vendolis/BeadSorter/STLs/2_Sequencer_base_modified_v2.stl

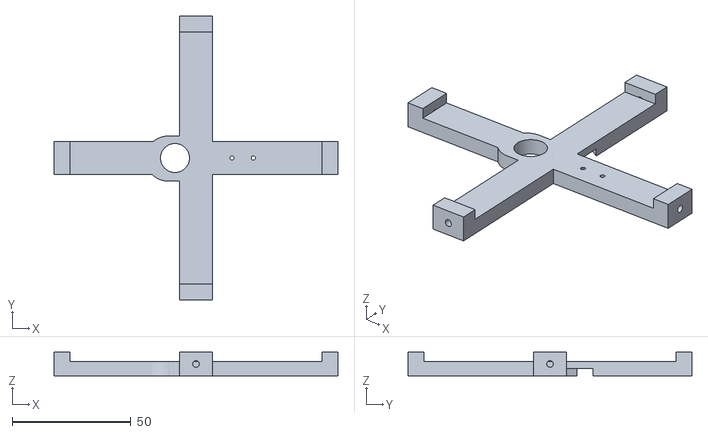
[picture p17: CAD file, 2026-03-10]
STLs/2_Sequencer_base_modified_v2.stl
119.6 x 119.6 x 10.0
