vendolis/BeadSorter/STLs/4-dispatcher-Tube-alignment-ring.stl

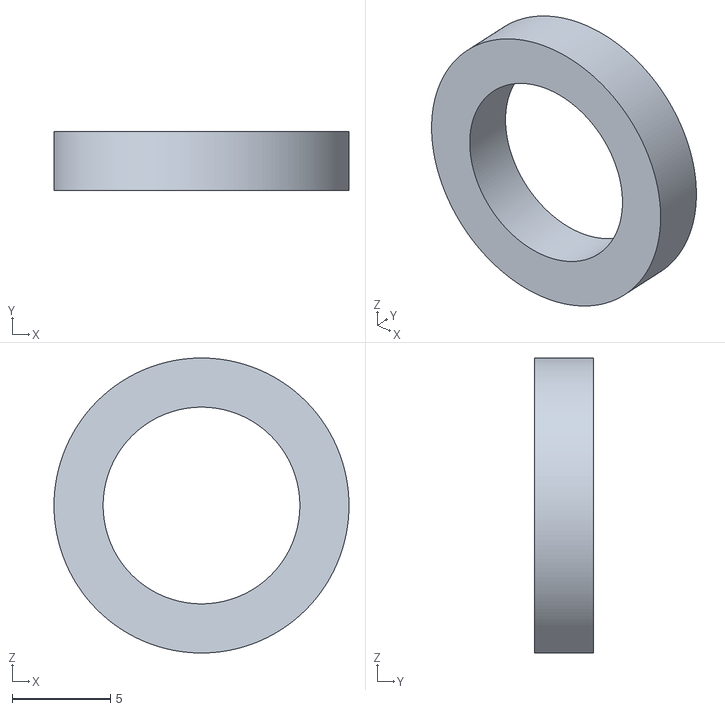
[picture p18: CAD file, 2026-03-10]
STLs/4-dispatcher-Tube-alignment-ring.stl
15.0 x 3.00 x 15.0
