vendolis/BeadSorter/STLs/4-dispatcher-Stepper-shaft.stl

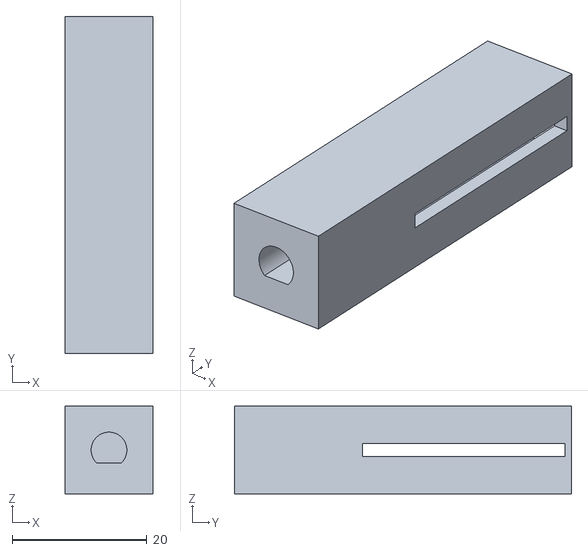
[picture p19: CAD file, 2026-03-10]
STLs/4-dispatcher-Stepper-shaft.stl
13.0 x 50.0 x 13.0
