vendolis/BeadSorter/STLs/5-outputs-slidePlate-holder_Typeb.stl

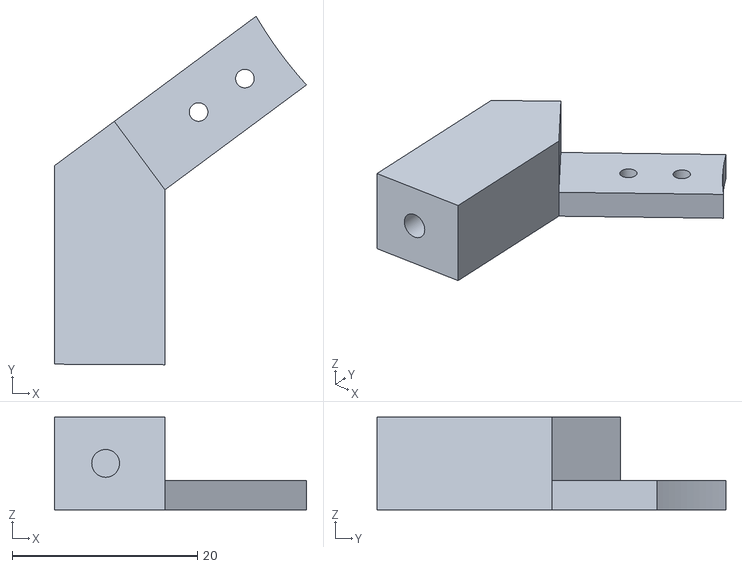
[picture p20: CAD file, 2026-03-10]
STLs/5-outputs-slidePlate-holder_Typeb.stl
27.2 x 37.6 x 10.0
