vendolis/BeadSorter/STLs/4-dispatcher-tube.stl

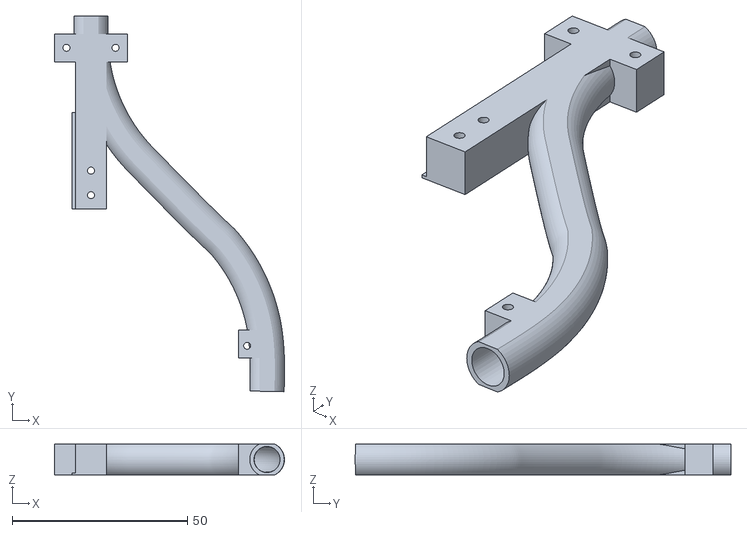
[picture p21: CAD file, 2026-03-09]
STLs/4-dispatcher-tube.stl
65.5 x 107.0 x 8.80
