vendolis/BeadSorter/STLs/4-dispatcher-tubehalf-1_modified.stl

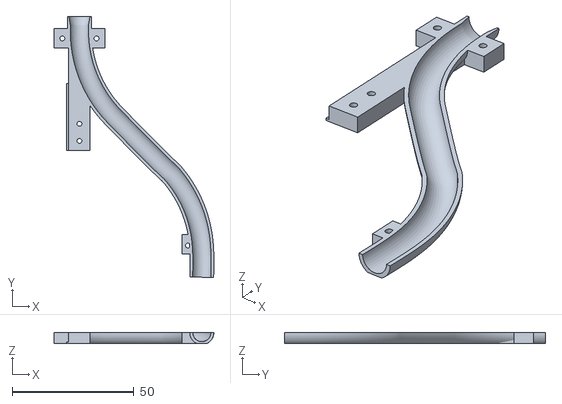
[picture p22: CAD file, 2026-03-09]
STLs/4-dispatcher-tubehalf-1_modified.stl
65.5 x 107.0 x 4.40
