vendolis/BeadSorter/STLs/3-analyzer-entry-tube_Extended.stl

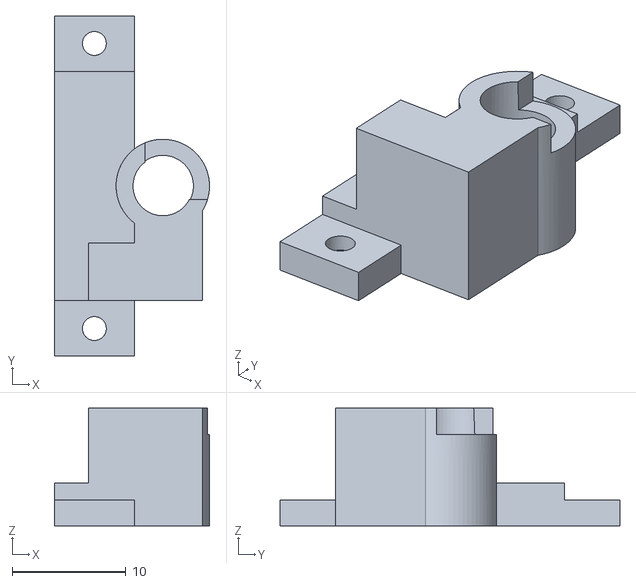
[picture p23: CAD file, 2026-03-09]
STLs/3-analyzer-entry-tube_Extended.stl
13.6 x 29.8 x 10.4
