vendolis/BeadSorter/STLs/2_Sequencer_tube_modified_v4_AntiStall.stl

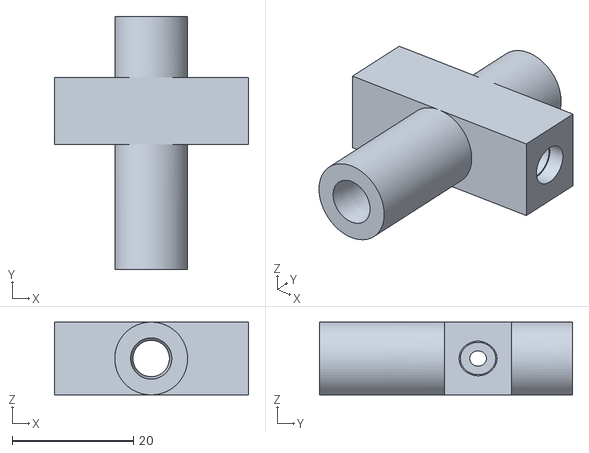
[picture p24: CAD file, 2026-03-09]
STLs/2_Sequencer_tube_modified_v4_AntiStall.stl
32.0 x 41.7 x 12.0
