vendolis/BeadSorter/STLs/SectionBracketPegs_v2.stl

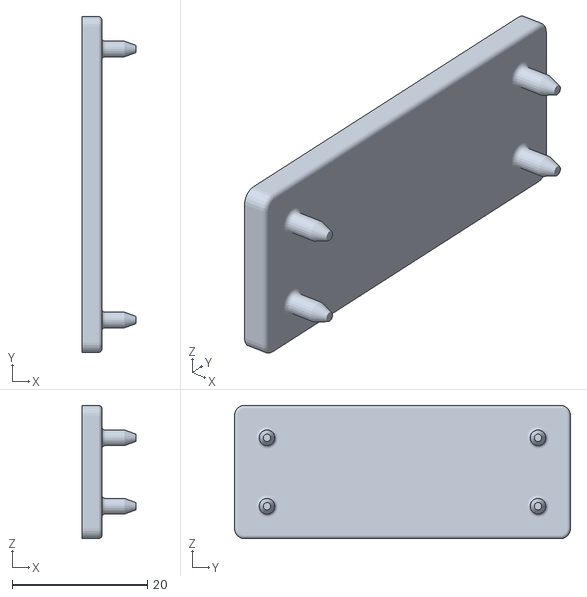
[picture p25: CAD file, 2026-03-09]
STLs/SectionBracketPegs_v2.stl
7.90 x 49.6 x 19.7
