vendolis/BeadSorter/STLs/0_HopperStick Holder v2.stl

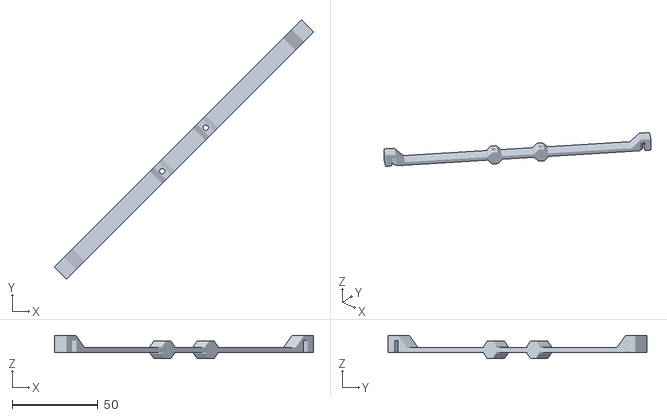
[picture p26: CAD file, 2026-03-09]
STLs/0_HopperStick Holder v2.stl
151.4 x 151.4 x 13.7
