vendolis/BeadSorter/STLs/SectionBracketHoles.stl

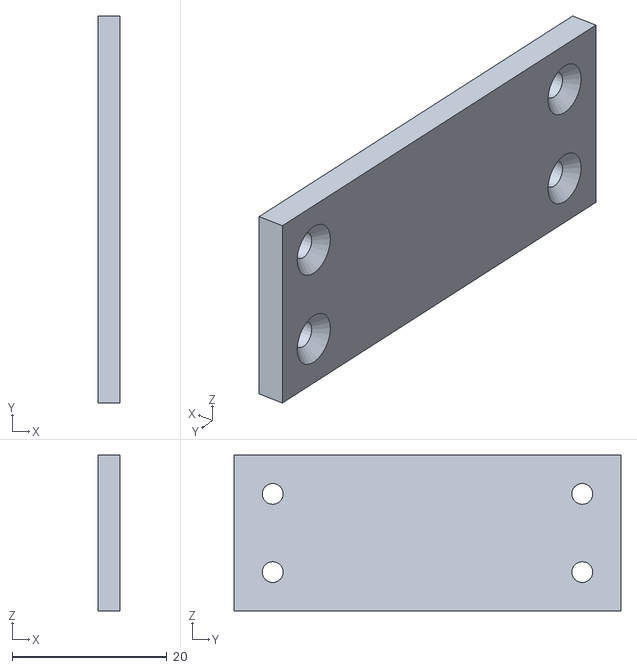
[picture p27: CAD file, 2026-03-09]
STLs/SectionBracketHoles.stl
2.90 x 50.0 x 20.1
