vendolis/BeadSorter/STLs/hopper-seq-plate-4_holes_modified_Glides.stl

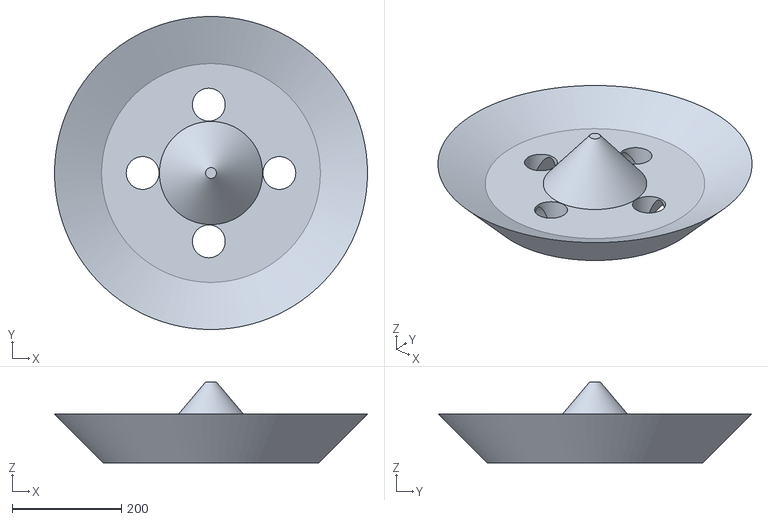
[picture p28: CAD file, 2026-03-09]
STLs/hopper-seq-plate-4_holes_modified_Glides.stl
572.3 x 572.3 x 147.9
