vendolis/BeadSorter/STLs/1-sequentializer-motor-holder.stl

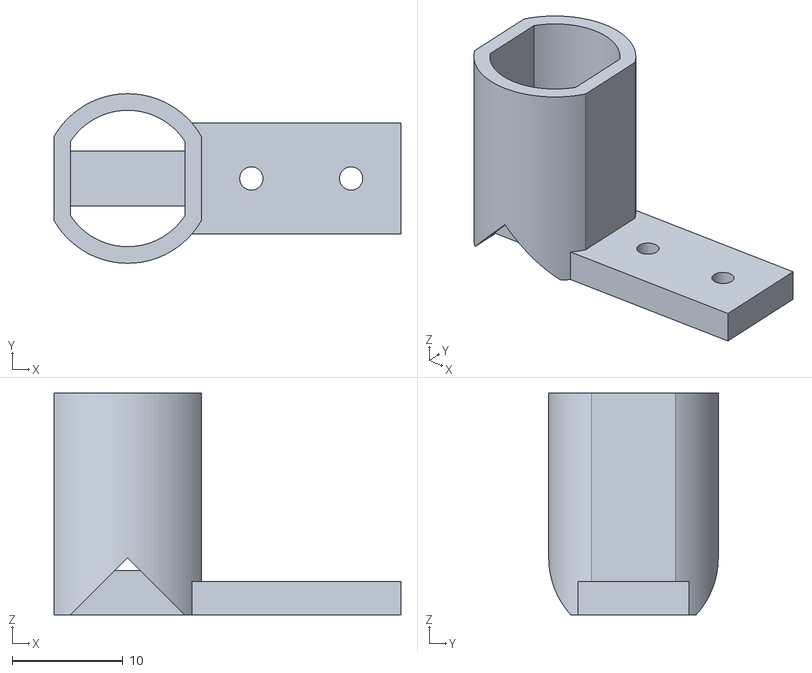
[picture p29: CAD file, 2026-03-05]
STLs/1-sequentializer-motor-holder.stl
31.3 x 15.3 x 20.0
