vendolis/BeadSorter/STLs/3-analyzer-ilc-top.stl

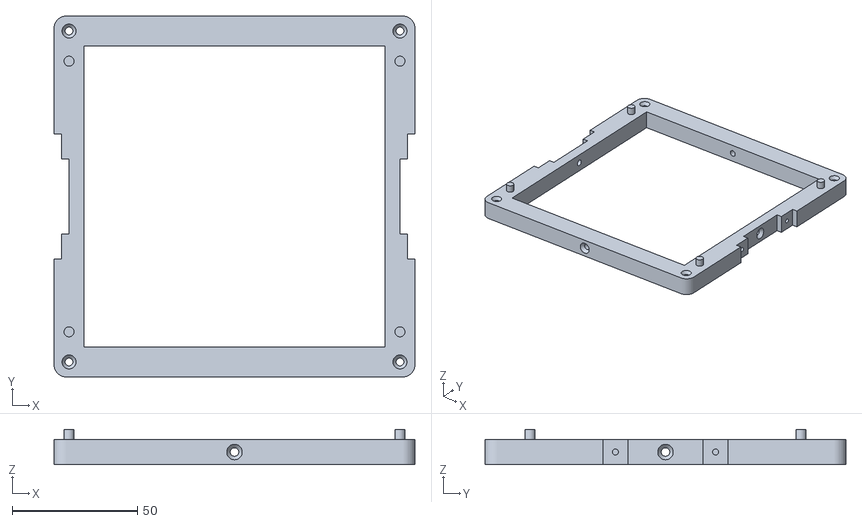
[picture p30: CAD file, 2026-03-05]
STLs/3-analyzer-ilc-top.stl
144.0 x 144.0 x 14.0
