vendolis/BeadSorter/STLs/3-analyzer-servo-holder.stl

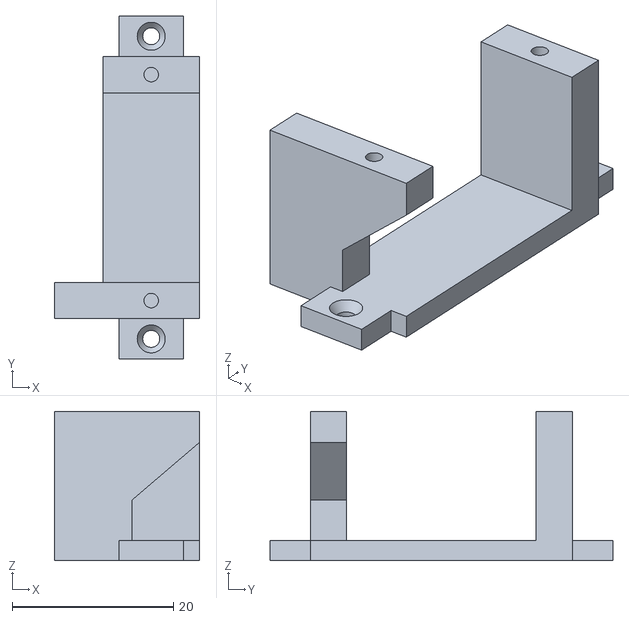
[picture p31: CAD file, 2026-03-05]
STLs/3-analyzer-servo-holder.stl
18.0 x 42.5 x 18.5
