vendolis/BeadSorter/STLs/0-hopper-seq-plate-4_holes_modified.stl

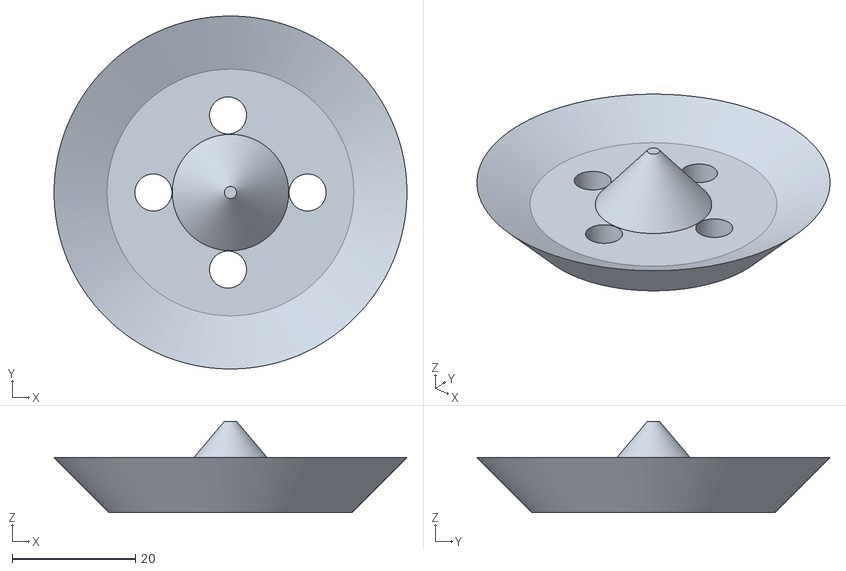
[picture p32: CAD file, 2026-03-05]
STLs/0-hopper-seq-plate-4_holes_modified.stl
57.2 x 57.2 x 14.8
