vendolis/BeadSorter/STLs/0-Hopper_Modified_Cleaned_up.stl

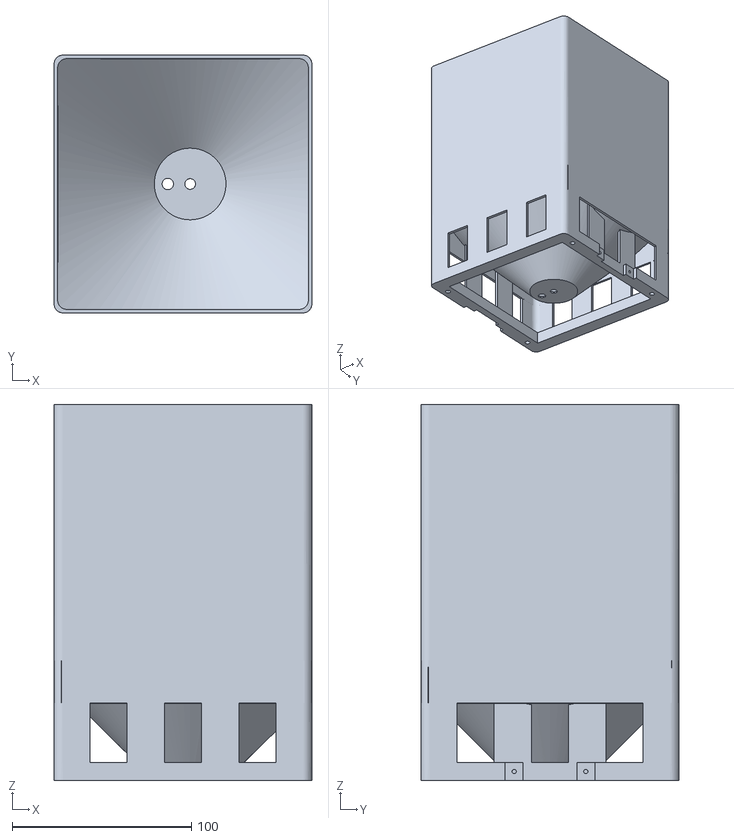
[picture p33: CAD file, 2026-03-05]
STLs/0-Hopper_Modified_Cleaned_up.stl
144.0 x 144.0 x 210.0
