vendolis/BeadSorter/STLs/4-dispatcher-tubehalf-2.stl

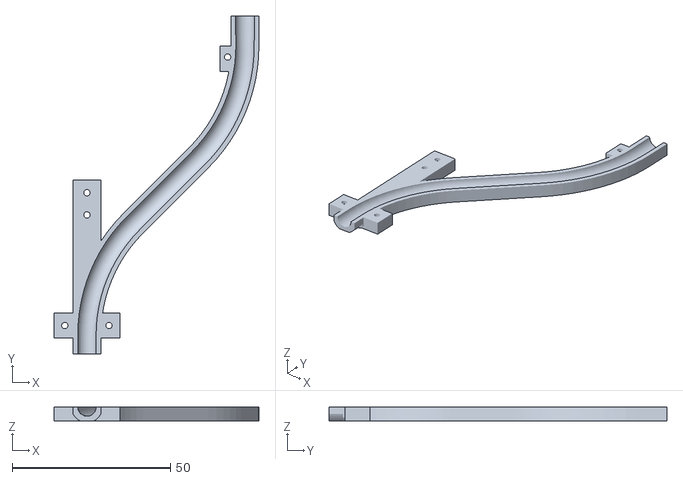
[picture p34: CAD file, 2026-03-05]
STLs/4-dispatcher-tubehalf-2.stl
64.8 x 106.9 x 4.40
