vendolis/BeadSorter/STLs/1-sequentializer-ilc-bottom.stl

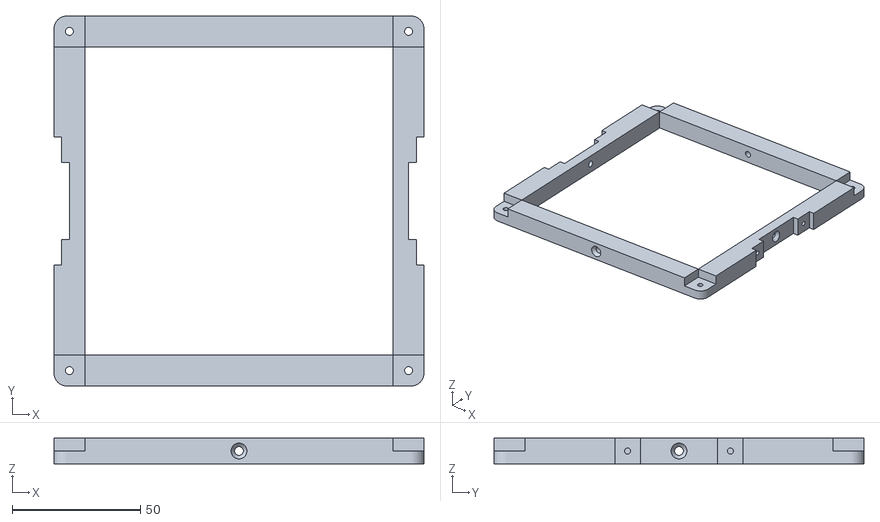
[picture p35: CAD file, 2026-03-05]
STLs/1-sequentializer-ilc-bottom.stl
144.0 x 144.0 x 10.0
