vendolis/BeadSorter/STLs/4-dispatcher-ilc-corner.stl

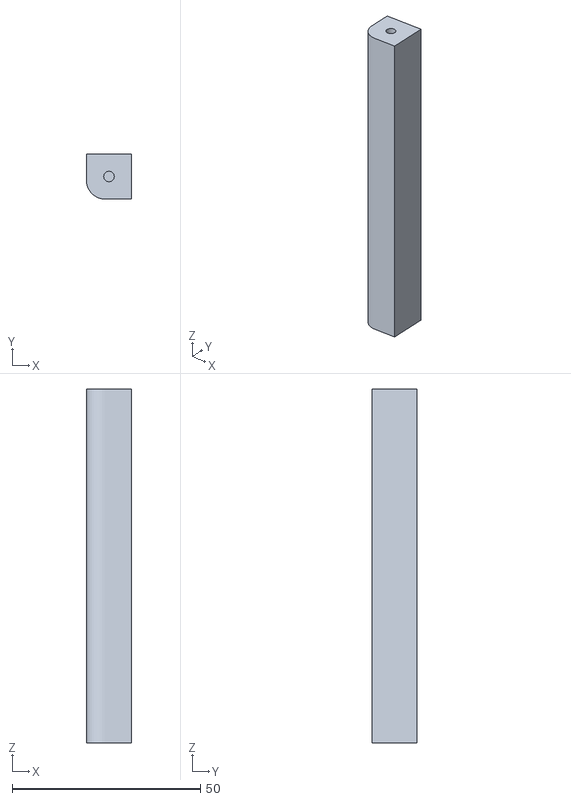
[picture p36: CAD file, 2026-03-05]
STLs/4-dispatcher-ilc-corner.stl
12.0 x 12.0 x 93.9
