vendolis/BeadSorter/STLs/4-dispatcher-ilc-bottom.stl

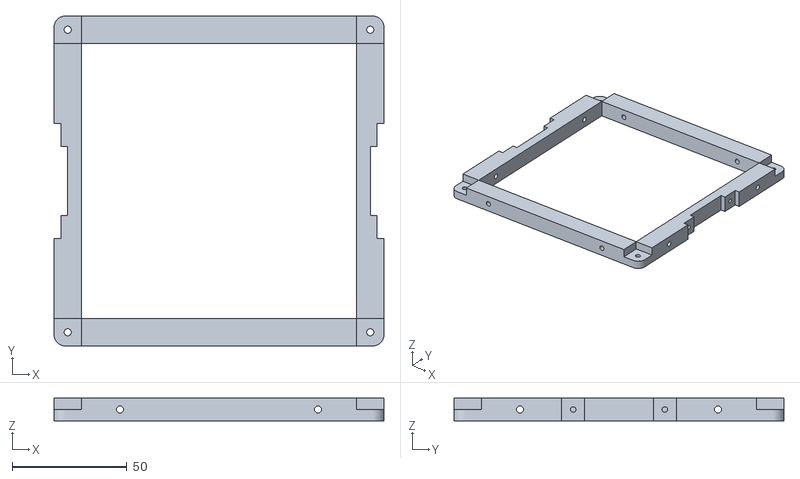
[picture p37: CAD file, 2026-03-05]
STLs/4-dispatcher-ilc-bottom.stl
144.0 x 144.0 x 10.0
