vendolis/BeadSorter/STLs/3-analyzer-exit-tube.stl

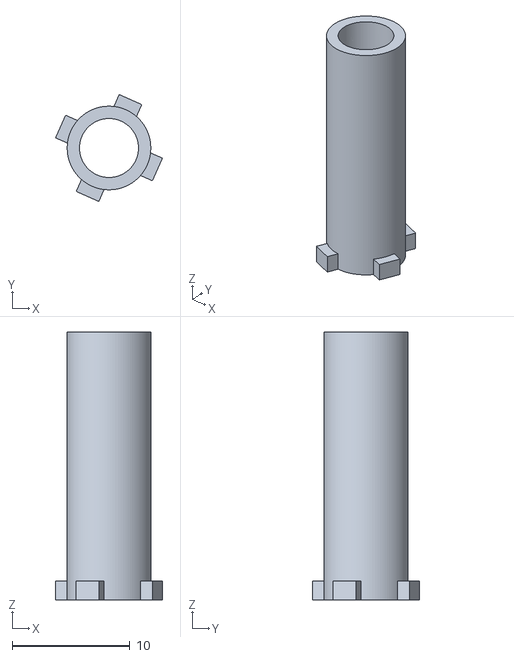
[picture p38: CAD file, 2026-03-05]
STLs/3-analyzer-exit-tube.stl
9.08 x 9.08 x 22.8
