vendolis/BeadSorter/STLs/5-outputs-ilc-corner.stl

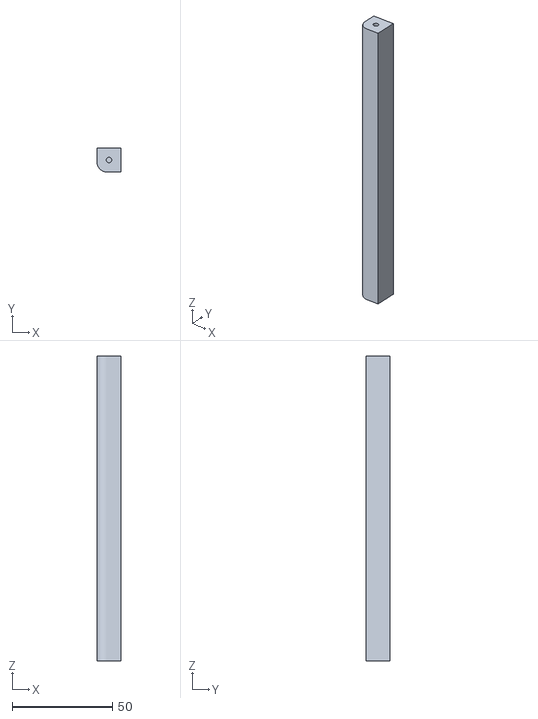
[picture p39: CAD file, 2026-03-05]
STLs/5-outputs-ilc-corner.stl
12.0 x 12.0 x 152.0
