vendolis/BeadSorter/STLs/3-analyzer-ilc-corner.stl

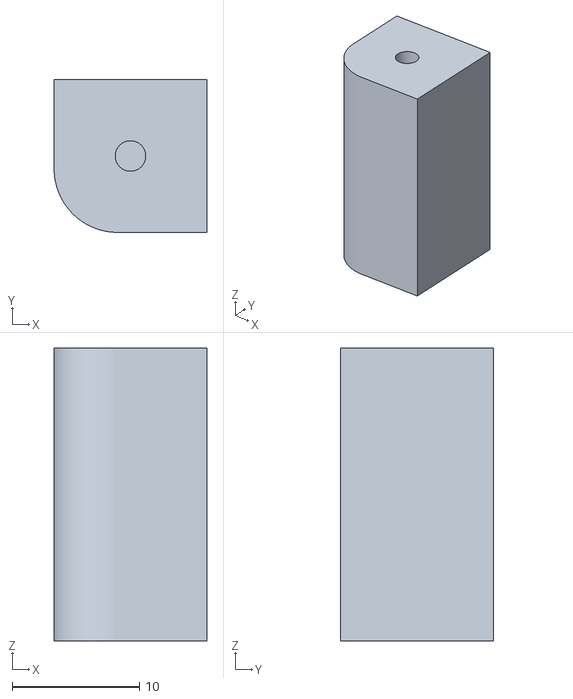
[picture p40: CAD file, 2026-03-05]
STLs/3-analyzer-ilc-corner.stl
12.0 x 12.0 x 23.1
