vendolis/BeadSorter/STLs/4-dispatcher-Stepper-shaft_alternative_3mm_square-Körper.stl

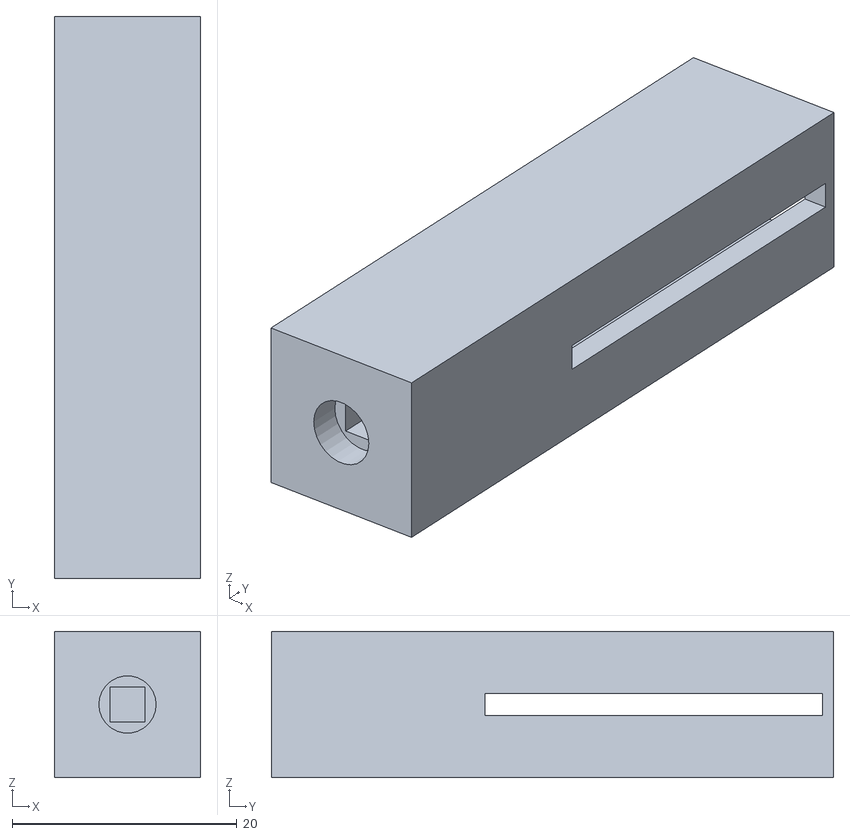
[picture p41: CAD file, 2026-03-05]
STLs/4-dispatcher-Stepper-shaft_alternative_3mm_square-Körper.stl
13.0 x 50.0 x 13.0
