vendolis/BeadSorter/STLs/3-analyzer-top-alignment.stl

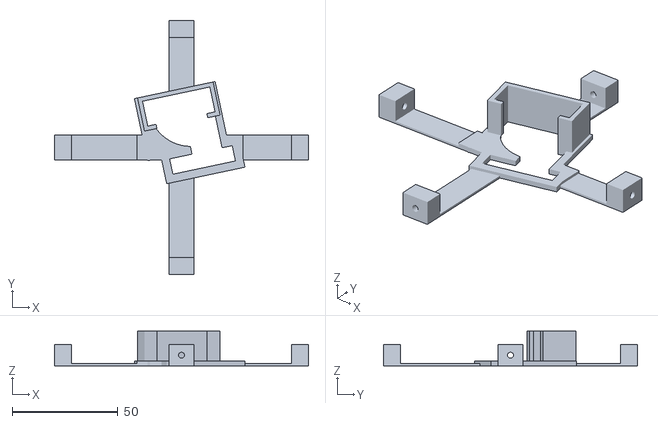
[picture p42: CAD file, 2026-03-05]
STLs/3-analyzer-top-alignment.stl
120.0 x 120.0 x 16.3
