vendolis/BeadSorter/STLs/0-hopper-seq-stopper.stl

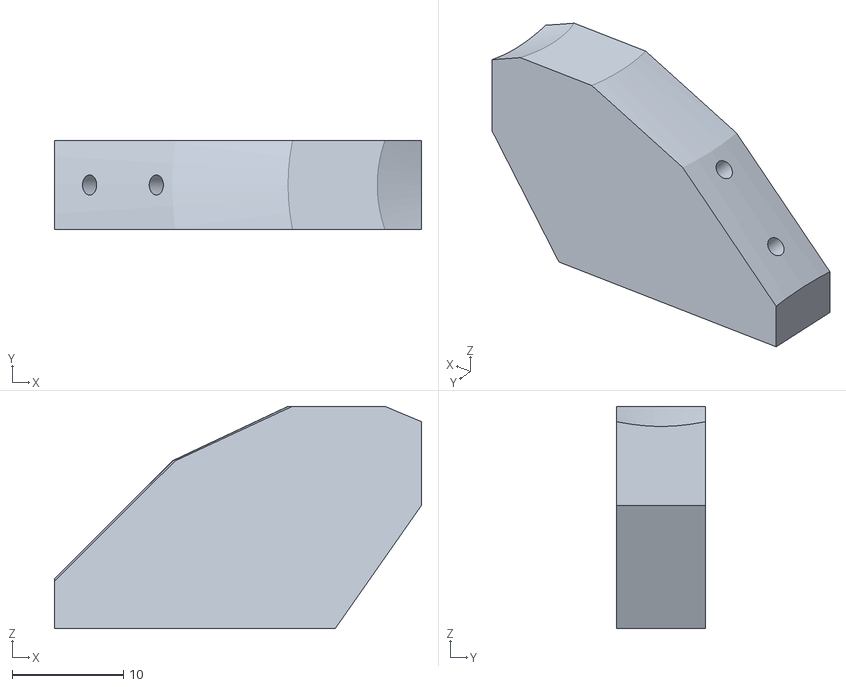
[picture p43: CAD file, 2026-03-05]
STLs/0-hopper-seq-stopper.stl
33.0 x 8.00 x 20.0
