vendolis/BeadSorter/STLs/4-dispatcher-tube-alignment.stl

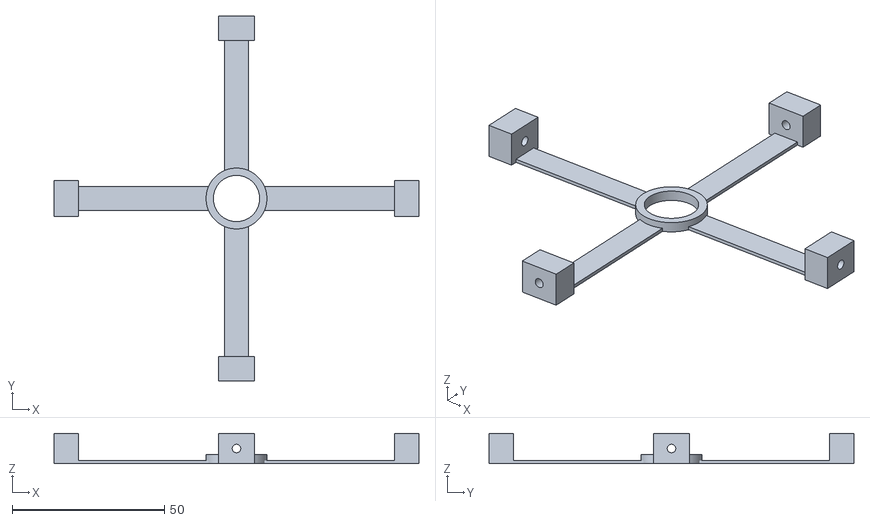
[picture p44: CAD file, 2026-03-05]
STLs/4-dispatcher-tube-alignment.stl
120.0 x 120.0 x 10.00
