vendolis/BeadSorter/classify_bead.py

import math


# Null scan baseline (empty chamber readings)
NULL_R = 498.1
NULL_G = 372.2
NULL_B = 244.2

# Max corrected RGB value (for scaling to 0-1)
RGB_MAX = 7931.9

# Normalization parameters (mean, std) for each feature
NORM_H_SIN = (0.470533, 0.356254)
NORM_H_COS = (0.488719, 0.642882)
NORM_S = (0.415330, 0.189916)
NORM_L = (0.191847, 0.165316)

# Representative points: (cluster_id, H_sin, H_cos, S, L)
# These are in the ORIGINAL (unnormalized) feature space.
REPRESENTATIVES = [
    (0, 0.981397, 0.191989, 0.458726, 0.240332),
    (0, 0.981061, 0.193701, 0.460193, 0.275317),
    (0, 0.966849, 0.255347, 0.448422, 0.228985),
    (0, 0.964240, 0.265030, 0.453953, 0.257856),
    (0, 0.964255, 0.264975, 0.455514, 0.185427),
    (1, 0.992586, 0.121547, 0.350025, 0.327574),
    (1, 0.939883, -0.341498, 0.265038, 0.354364),
    (1, 0.993824, 0.110967, 0.343485, 0.360605),
    (1, 0.988113, -0.153728, 0.352519, 0.313454),
    (1, 0.992391, 0.123125, 0.342631, 0.289752),
    (2, 0.891929, 0.452175, 0.231817, 0.381218),
    (2, 0.959937, 0.280216, 0.227916, 0.461589),
    (2, 0.929334, 0.369241, 0.230818, 0.440220),
    (2, 0.929025, 0.370016, 0.227779, 0.388530),
    (2, 0.960432, 0.278516, 0.241869, 0.412547),
    (3, 0.920954, -0.389671, 0.412970, 0.079211),
    (3, 0.972815, -0.231584, 0.352991, 0.100706),
    (3, 0.951580, -0.307401, 0.393046, 0.091566),
    (3, 0.987681, 0.156480, 0.333548, 0.020965),
    (3, 0.930853, -0.365393, 0.320121, 0.075996),
    (4, 0.585068, -0.810984, 0.380327, 0.184110),
    (4, 0.547077, -0.837082, 0.417597, 0.143074),
    (4, 0.544982, -0.838448, 0.393963, 0.157257),
    (4, 0.572035, -0.820230, 0.379107, 0.127504),
    (4, 0.583186, -0.812339, 0.404314, 0.165704),
    (5, 0.894990, -0.446087, 0.142407, 0.000857),
    (5, 0.894990, -0.446087, 0.124142, 0.000983),
    (5, 0.894990, -0.446087, 0.142407, 0.000857),
    (5, 0.894990, -0.446087, 0.142407, 0.000857),
    (5, 0.894990, -0.446087, 0.142407, 0.000857),
    (6, 0.922234, -0.386632, 0.074308, 0.000794),
    (6, 0.922234, -0.386632, 0.074308, 0.000794),
    (6, 0.922234, -0.386632, 0.074308, 0.000794),
    (6, 0.922234, -0.386632, 0.074308, 0.000794),
    (6, 0.922234, -0.386632, 0.074308, 0.000794),
    (7, 0.922234, -0.386632, 0.064124, 0.000920),
    (7, 0.922234, -0.386632, 0.064124, 0.000920),
    (7, 0.922234, -0.386632, 0.064124, 0.000920),
    (7, 0.922234, -0.386632, 0.064124, 0.000920),
    (7, 0.922234, -0.386632, 0.064124, 0.000920),
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
]

K_NEIGHBORS = 3


def _rgb_to_hls(r, g, b):
    """Convert RGB (0-1) to HLS. Returns (h, l, s)."""
    max_c = max(r, g, b)
    min_c = min(r, g, b)
    l = (max_c + min_c) / 2.0

    if max_c == min_c:
        return (0.0, l, 0.0)

    d = max_c - min_c
    s = d / (2.0 - max_c - min_c) if l > 0.5 else d / (max_c + min_c)

    if max_c == r:
        h = (g - b) / d + (6.0 if g < b else 0.0)
    elif max_c == g:
        h = (b - r) / d + 2.0
    else:
        h = (r - g) / d + 4.0
    h /= 6.0

    return (h, l, s)


def classify_bead(raw_r, raw_g, raw_b, raw_c):
    """
    Classify a bead from raw TCS34725 sensor values.

    Args:
        raw_r, raw_g, raw_b, raw_c: Raw RGBC readings from the sensor.

    Returns:
        Cluster ID (0-37), or -1 if the reading looks like an empty chamber.
    """
    # Subtract ambient light baseline
    r_corr = max(raw_r - NULL_R, 1.0)
    g_corr = max(raw_g - NULL_G, 1.0)
    b_corr = max(raw_b - NULL_B, 1.0)

    # Check if this is an empty chamber (values close to null baseline)
    if r_corr + g_corr + b_corr < 50:
        return -1

    # Scale to 0-1
    r01 = r_corr / RGB_MAX
    g01 = g_corr / RGB_MAX
    b01 = b_corr / RGB_MAX

    # Convert to HLS
    h, l, s = _rgb_to_hls(r01, g01, b01)

    # Encode hue on unit circle
    h_sin = math.sin(2.0 * math.pi * h)
    h_cos = math.cos(2.0 * math.pi * h)

    # Normalize features
    h_sin_n = (h_sin - NORM_H_SIN[0]) / NORM_H_SIN[1]
    h_cos_n = (h_cos - NORM_H_COS[0]) / NORM_H_COS[1]
    s_n = (s - NORM_S[0]) / NORM_S[1]
    l_n = (l - NORM_L[0]) / NORM_L[1]

    # Find k nearest neighbors by Euclidean distance
    distances = []
    for cluster_id, rep_h_sin, rep_h_cos, rep_s, rep_l in REPRESENTATIVES:
        # Normalize the representative point
        rh_sin_n = (rep_h_sin - NORM_H_SIN[0]) / NORM_H_SIN[1]
        rh_cos_n = (rep_h_cos - NORM_H_COS[0]) / NORM_H_COS[1]
        rs_n = (rep_s - NORM_S[0]) / NORM_S[1]
        rl_n = (rep_l - NORM_L[0]) / NORM_L[1]

        dist = math.sqrt(
            (h_sin_n - rh_sin_n) ** 2
            + (h_cos_n - rh_cos_n) ** 2
            + (s_n - rs_n) ** 2
            + (l_n - rl_n) ** 2
        )
        distances.append((dist, cluster_id))

    # Sort by distance, take k nearest
    distances.sort()
    neighbors = distances[:K_NEIGHBORS]

    # Distance-weighted vote
    votes = {}
    for dist, cluster_id in neighbors:
        weight = 1.0 / (dist + 1e-9)
        votes[cluster_id] = votes.get(cluster_id, 0.0) + weight

    return max(votes, key=votes.get)


if __name__ == "__main__":
    # Quick test with a few raw values from the log
    test_beads = [
        (993, 1529, 1222, 3789),    # Bead #0
        (4587, 2046, 1105, 7719),   # Bead #1
        (1586, 2418, 1969, 5961),   # Bead #2
        (1422, 1730, 1626, 4733),   # Bead #3
        (507, 381, 249, 1146),      # Null scan (should return -1)
    ]
    for r, g, b, c in test_beads:
        result = classify_bead(r, g, b, c)
        print(f"  R={r:5d} G={g:5d} B={b:5d} C={c:5d}  -> Cluster {result}")
