vendolis/BeadSorter/analyse_beads.py

#!/usr/bin/env python3
"""
analyse_beads.py — BeadSorter colour-space analysis tool
=========================================================

Reads the CSV produced by BeadCalibrate.ino and answers:
  1. Which TCS34725 gain setting gives clean, stable readings (no saturation,
     low intra-bead variance)?
  2. Which colour space — HSL, Chromaticity, Normalized RGB — best separates
     the scanned bead colours (maximum minimum pairwise distance)?
  3. What per-channel thresholds should go into BeadSorter.ino?

Usage:
  python analyse_beads.py  beads.csv
  python analyse_beads.py  beads.csv  --gain g16x
  python analyse_beads.py  beads.csv  --top 15

Output sections:
  • Saturation summary (per gain)
  • Per-bead mean values table (per gain)
  • Pairwise distance table — closest pairs first (per gain × colour space)
  • Cross-gain separability comparison
  • Threshold recommendations for BeadSorter.ino

Lines starting with '#' in the CSV are treated as comments and ignored.

Colour spaces compared
----------------------
  HSL       — H (circular), S, L  (same as BeadSorter.ino currently uses)
  HS        — H (circular), S only  (tests whether L helps or hurts)
  Chroma2   — chroma_r, chroma_g  (ambient-independent 2-D chromaticity)
  Chroma3   — chroma_r, chroma_g, chroma_b  (3-D; redundant since r+g+b=1
              but included for completeness)
  NormRGB   — R_norm, G_norm, B_norm  (clear-normalised, 0-255 scale)

Scale note — why raw distances cannot be compared across colour spaces
----------------------------------------------------------------------
  NormRGB operates on a 0-255 axis scale while all other spaces use 0-1,
  so raw Euclidean distances differ by a factor of up to ~255.  A NormRGB
  distance of 1.8 is NOT larger than a Chroma2 distance of 0.005 — they
  live on completely different rulers.

  The correct comparison metric is SNR (signal-to-noise ratio):

      SNR = min inter-bead distance / intra-bead noise RMS

  where noise RMS = sqrt(Σ avg_bead(σ_dim²)) across all dimensions of the
  space.  This is dimensionless and scale-independent.  An SNR > ~3 means
  beads are separated by more than 3× the typical sensor jitter — reliably
  classifiable.  All tables and the final recommendation use SNR.

Notes
-----
  - Chroma2 is usually best for this sensor because it is immune to absolute
    brightness variation and captures hue+saturation in a single 2-D metric.
  - HSL is good when hue spans a wide arc; it degrades for low-saturation
    colours where hue is poorly defined / noisy.
  - 16x gain often saturates bright reds/whites; if saturation % is high,
    prefer 4x or 1x for those beads.
"""

import sys
import io
import csv
import math
import collections
import itertools
import argparse
import statistics

# Ensure UTF-8 output on Windows terminals that default to cp1252.
if hasattr(sys.stdout, "reconfigure"):
    sys.stdout.reconfigure(encoding="utf-8", errors="replace")

# ── Circular hue helpers ──────────────────────────────────────────────────────

def hue_dist(h1: float, h2: float) -> float:
    """Shortest angular distance between two hue values in [0, 1]."""
    d = abs(h1 - h2)
    return min(d, 1.0 - d)


def circular_mean_hue(hues) -> float:
    """Compute the circular mean of hue values in [0, 1]."""
    sin_sum = sum(math.sin(h * 2.0 * math.pi) for h in hues)
    cos_sum = sum(math.cos(h * 2.0 * math.pi) for h in hues)
    angle = math.atan2(sin_sum, cos_sum)
    if angle < 0.0:
        angle += 2.0 * math.pi
    return angle / (2.0 * math.pi)


# ── Distance functions (one per colour space) ─────────────────────────────────

def dist_hsl(a: dict, b: dict) -> float:
    dh = hue_dist(a["H"], b["H"])
    return math.sqrt(dh**2 + (a["S"] - b["S"])**2 + (a["L"] - b["L"])**2)


def dist_hs(a: dict, b: dict) -> float:
    """HSL without L — tests whether lightness adds discriminating power."""
    dh = hue_dist(a["H"], b["H"])
    return math.sqrt(dh**2 + (a["S"] - b["S"])**2)


def dist_chroma2(a: dict, b: dict) -> float:
    """2-D chromaticity: chroma_r and chroma_g only (chroma_b = 1 - r - g)."""
    return math.sqrt((a["chroma_r"] - b["chroma_r"])**2 +
                     (a["chroma_g"] - b["chroma_g"])**2)


def dist_chroma3(a: dict, b: dict) -> float:
    """3-D chromaticity: all three normalised colour fractions."""
    return math.sqrt((a["chroma_r"] - b["chroma_r"])**2 +
                     (a["chroma_g"] - b["chroma_g"])**2 +
                     (a["chroma_b"] - b["chroma_b"])**2)


def dist_normrgb(a: dict, b: dict) -> float:
    """Euclidean distance in clear-normalised RGB space (0-255 scale)."""
    return math.sqrt((a["R_norm"] - b["R_norm"])**2 +
                     (a["G_norm"] - b["G_norm"])**2 +
                     (a["B_norm"] - b["B_norm"])**2)


# Ordered dict so the table columns stay consistent.
COLOR_SPACES = {
    "HSL":     dist_hsl,
    "HS":      dist_hs,
    "Chroma2": dist_chroma2,
    "Chroma3": dist_chroma3,
    "NormRGB": dist_normrgb,
}

# std_* fields that contribute to each space's noise RMS estimate.
# Must match the dimensions used in the corresponding dist_* function.
CS_STD_FIELDS = {
    "HSL":     ["std_H", "std_S", "std_L"],
    "HS":      ["std_H", "std_S"],
    "Chroma2": ["std_chroma_r", "std_chroma_g"],
    "Chroma3": ["std_chroma_r", "std_chroma_g", "std_chroma_b"],
    "NormRGB": ["std_R_norm", "std_G_norm", "std_B_norm"],
}


def cs_noise_rms(means: dict, cs_name: str) -> float:
    """
    Typical intra-bead positional noise magnitude for a given colour space.

    Computed as sqrt(Σ_dim  mean_bead(σ_dim²)) — the expected Euclidean
    distance between a bead's true colour-space position and one noisy
    measurement.  Scale-aware: directly comparable to the same space's
    dist_* output, so dividing distance / noise_rms gives a dimensionless
    SNR that can be compared across colour spaces and gains.

    Only beads with ≥2 samples (which carry std fields) contribute.
    Returns NaN if none qualify.
    """
    std_fields = CS_STD_FIELDS[cs_name]
    qualifying = [m for m in means.values() if std_fields[0] in m]
    if not qualifying:
        return float("nan")
    return math.sqrt(sum(
        statistics.mean(m[f] ** 2 for m in qualifying)
        for f in std_fields
    ))

# ── CSV parsing ───────────────────────────────────────────────────────────────

def parse_csv(path: str) -> list:
    rows = []
    with open(path, newline="", encoding="utf-8") as fh:
        lines = fh.readlines()

    # Find the actual CSV header — first non-comment line containing 'bead,gain'.
    header_idx = None
    for i, line in enumerate(lines):
        if line.lstrip().startswith("#"):
            continue
        if "bead" in line and "gain" in line and "sample" in line:
            header_idx = i
            break
    if header_idx is None:
        return rows

    # Keep header + data lines; drop comment lines.
    data_lines = [lines[header_idx]] + [
        l for l in lines[header_idx + 1:]
        if not l.lstrip().startswith("#")
    ]
    reader = csv.DictReader(io.StringIO("".join(data_lines)))
    for row in reader:
            try:
                entry = {
                    "bead":     int(row["bead"]),
                    "gain":     row["gain"].strip(),
                    "sample":   int(row["sample"]),
                    "R_raw":    int(row["R_raw"]),
                    "G_raw":    int(row["G_raw"]),
                    "B_raw":    int(row["B_raw"]),
                    "C_raw":    int(row["C_raw"]),
                    "sat":      int(row["saturated"]) != 0,
                    "R_norm":   float(row["R_norm"]),
                    "G_norm":   float(row["G_norm"]),
                    "B_norm":   float(row["B_norm"]),
                    "chroma_r": float(row["chroma_r"]),
                    "chroma_g": float(row["chroma_g"]),
                    "chroma_b": float(row["chroma_b"]),
                    "H":        float(row["H"]),
                    "S":        float(row["S"]),
                    "L":        float(row["L"]),
                }
                rows.append(entry)
            except (KeyError, ValueError):
                pass  # skip malformed rows silently
    return rows

# ── Per-bead statistics ───────────────────────────────────────────────────────

SCALAR_FIELDS = ["R_norm", "G_norm", "B_norm",
                 "chroma_r", "chroma_g", "chroma_b",
                 "S", "L"]


def compute_bead_means(rows: list, gain: str) -> dict:
    """
    Return {bead_id: mean_dict} for the given gain, excluding saturated rows.
    mean_dict contains mean values for every colour field plus 'n' (sample count).
    """
    filtered = [r for r in rows if r["gain"] == gain and not r["sat"]]
    by_bead = collections.defaultdict(list)
    for r in filtered:
        by_bead[r["bead"]].append(r)

    means = {}
    for bead, rs in sorted(by_bead.items()):
        m = {"bead": bead, "n": len(rs)}
        m["H"] = circular_mean_hue([r["H"] for r in rs])
        for f in SCALAR_FIELDS:
            m[f] = statistics.mean(r[f] for r in rs)
        # Intra-bead noise (std dev); needs ≥ 2 samples.
        if len(rs) >= 2:
            m["std_H"] = statistics.stdev(r["H"] for r in rs)
            for f in SCALAR_FIELDS:
                m[f"std_{f}"] = statistics.stdev(r[f] for r in rs)
        means[bead] = m
    return means


# ── Pairwise analysis ─────────────────────────────────────────────────────────

def pairwise_distances(means: dict, dist_fn) -> list:
    """Return sorted list of (distance, bead_a, bead_b) for all pairs."""
    pairs = [
        (dist_fn(means[a], means[b]), a, b)
        for a, b in itertools.combinations(sorted(means.keys()), 2)
    ]
    pairs.sort()
    return pairs


def suggest_hsl_thresholds(means: dict) -> tuple:
    """
    Return (thH, thS, thL) as half the minimum per-channel inter-bead gap.
    This is the tightest threshold that does not split any pair.

    Note: this is computed per-channel independently (AND-logic matching).
    A pair separated by one channel won't be penalised in another channel's gap.
    """
    beads = sorted(means.keys())
    min_dH = min_dS = min_dL = float("inf")
    for a, b in itertools.combinations(beads, 2):
        dh = hue_dist(means[a]["H"], means[b]["H"])
        ds = abs(means[a]["S"] - means[b]["S"])
        dl = abs(means[a]["L"] - means[b]["L"])
        if dh < min_dH:
            min_dH = dh
        if ds < min_dS:
            min_dS = ds
        if dl < min_dL:
            min_dL = dl
    return min_dH / 2.0, min_dS / 2.0, min_dL / 2.0


def suggest_chroma_threshold(means: dict) -> float:
    """Return half the minimum 2-D chromaticity distance between any pair."""
    beads = sorted(means.keys())
    min_d = min(
        dist_chroma2(means[a], means[b])
        for a, b in itertools.combinations(beads, 2)
    )
    return min_d / 2.0


# ── Keep-together / keep-apart feasibility ───────────────────────────────────

def compute_hsl_deviations(rows: list, gain: str, means: dict) -> dict:
    """
    For each bead, compute the maximum per-channel deviation of any individual
    sample from the bead's computed mean (H circular, S/L linear).

    This is the MINIMUM threshold required to keep all readings of the same
    bead in the same bucket.

    Returns {bead: {'dH': float, 'dS': float, 'dL': float}}.
    """
    filtered = [r for r in rows if r["gain"] == gain and not r["sat"]]
    by_bead = collections.defaultdict(list)
    for r in filtered:
        by_bead[r["bead"]].append(r)

    devs = {}
    for bead, rs in by_bead.items():
        if bead not in means:
            continue
        m = means[bead]
        devs[bead] = {
            "dH": max(hue_dist(r["H"], m["H"]) for r in rs),
            "dS": max(abs(r["S"]  - m["S"])     for r in rs),
            "dL": max(abs(r["L"]  - m["L"])     for r in rs),
        }
    return devs


def compute_chroma2_deviations(rows: list, gain: str, means: dict) -> dict:
    """
    For each bead, compute the maximum 2-D chromaticity distance of any
    individual sample from the bead's mean.

    Returns {bead: float}.
    """
    filtered = [r for r in rows if r["gain"] == gain and not r["sat"]]
    by_bead = collections.defaultdict(list)
    for r in filtered:
        by_bead[r["bead"]].append(r)

    devs = {}
    for bead, rs in by_bead.items():
        if bead not in means:
            continue
        m = means[bead]
        devs[bead] = max(dist_chroma2(r, m) for r in rs)
    return devs


def hsl_classification_analysis(means: dict, hsl_devs: dict) -> None:
    """
    Print the keep-together / keep-apart feasibility table for HSL.

    For each channel Ch independently, and for each bead:
      spread_Ch   = max deviation of samples from the bead's own mean
                    → threshold must be ≥ this to keep the bead together
      margin_Ch   = distance to nearest neighbour in channel Ch
                    → threshold must be < margin_Ch/2 so the neighbour
                      does not accidentally match

    Because BeadSorter uses AND-logic (all channels must match), a bead pair
    can be separated by ANY single channel.  So the "effective margin" for a
    pair is the channel with the LARGEST effective gap:
      effective_gap(X,Y) = max over Ch of (|mean_X_Ch - mean_Y_Ch|
                                           - spread_X_Ch - spread_Y_Ch)

    If effective_gap > 0 for at least one channel, the pair is separable.
    """
    beads = sorted(means.keys())
    if not beads:
        return

    # ── Per-channel global summary ──────────────────────────────────────────
    channels = [
        ("H", lambda a, b: hue_dist(a["H"], b["H"])),
        ("S", lambda a, b: abs(a["S"] - b["S"])),
        ("L", lambda a, b: abs(a["L"] - b["L"])),
    ]

    print("\n  HSL per-channel threshold feasibility:")
    print(f"    {'Ch':2s}  {'min_T (spread)':>16s}  {'max_T (gap/2)':>14s}  "
          f"{'recommended':>12s}  status")
    sep()
    for ch_name, gap_fn in channels:
        dev_key = f"d{ch_name}"
        # min_T: the bead with the largest spread drives the lower bound
        worst_b = max((b for b in hsl_devs if b in means),
                      key=lambda b: hsl_devs[b][dev_key], default=None)
        min_T = hsl_devs[worst_b][dev_key] if worst_b else 0.0

        # max_T: half the smallest inter-bead gap in this channel
        min_gap = min(gap_fn(means[a], means[b])
                      for a, b in itertools.combinations(beads, 2))
        max_T = min_gap / 2.0

        if min_T < max_T:
            rec = (min_T + max_T) / 2.0
            status = "OK"
        elif min_T == 0.0:
            rec = max_T * 0.5
            status = "OK (no spread)"
        else:
            rec = float("nan")
            status = "INFEASIBLE"
        rec_str = f"{rec:.5f}" if not math.isnan(rec) else "   n/a"
        worst_str = f"(bead {worst_b})" if worst_b else ""
        print(f"    {ch_name:2s}  {min_T:>14.5f}  "
              f"{max_T:>14.5f}  {rec_str:>12s}  {status}  {worst_str}")

    # ── Per-bead-pair effective margin (AND-logic) ───────────────────────────
    print(f"\n  Per-pair AND-logic effective margin  "
          f"(positive = separable after accounting for spread):")
    print(f"    {'Pair':>12s}  {'dH gap':>8s}  {'dS gap':>8s}  {'dL gap':>8s}  "
          f"{'best gap':>9s}  status")
    sep()
    insep = []
    for a, b in itertools.combinations(beads, 2):
        dH_gap = hue_dist(means[a]["H"], means[b]["H"]) \
                 - hsl_devs.get(a, {}).get("dH", 0) \
                 - hsl_devs.get(b, {}).get("dH", 0)
        dS_gap = abs(means[a]["S"] - means[b]["S"]) \
                 - hsl_devs.get(a, {}).get("dS", 0) \
                 - hsl_devs.get(b, {}).get("dS", 0)
        dL_gap = abs(means[a]["L"] - means[b]["L"]) \
                 - hsl_devs.get(a, {}).get("dL", 0) \
                 - hsl_devs.get(b, {}).get("dL", 0)
        best = max(dH_gap, dS_gap, dL_gap)
        separable = best > 0
        if not separable:
            insep.append((a, b, best))
        warn = "  ← INSEPARABLE" if not separable else \
               ("  ← tight" if best < 0.005 else "")
        # Only print tight or inseparable pairs to keep output manageable
        if best < 0.015 or not separable:
            print(f"    {a:>5d} vs {b:>3d}  {dH_gap:>8.4f}  {dS_gap:>8.4f}  "
                  f"{dL_gap:>8.4f}  {best:>9.4f}{warn}")

    if insep:
        print(f"\n  !! {len(insep)} inseparable pair(s) in HSL — "
              f"no threshold can distinguish them reliably.")
    else:
        print(f"\n  All HSL pairs have at least one channel with positive margin.")


def chroma2_classification_analysis(means: dict, chroma_devs: dict) -> None:
    """
    Print keep-together / keep-apart feasibility for 2-D chromaticity.

    For each bead pair (X, Y):
      effective_gap = dist_chroma2(mean_X, mean_Y) - spread_X - spread_Y
    If > 0, a single Euclidean threshold can separate them.
    """
    beads = sorted(means.keys())
    if not beads:
        return

    worst_b = max((b for b in chroma_devs if b in means),
                  key=lambda b: chroma_devs[b], default=None)
    min_T = chroma_devs[worst_b] if worst_b else 0.0
    min_gap = min(dist_chroma2(means[a], means[b])
                  for a, b in itertools.combinations(beads, 2))
    max_T = min_gap / 2.0

    if min_T < max_T:
        rec = (min_T + max_T) / 2.0
        status = "OK"
    else:
        rec = float("nan")
        status = "INFEASIBLE"
    rec_str = f"{rec:.5f}" if not math.isnan(rec) else "n/a"

    print(f"\n  Chroma2 threshold feasibility:")
    print(f"    min_T (max spread, bead {worst_b}): {min_T:.5f}")
    print(f"    max_T (min inter-bead gap / 2):   {max_T:.5f}")
    print(f"    recommended threshold:            {rec_str}   [{status}]")

    print(f"\n  Per-pair Chroma2 effective margin:")
    print(f"    {'Pair':>12s}  {'inter dist':>10s}  {'spread X':>9s}  "
          f"{'spread Y':>9s}  {'eff. gap':>9s}  status")
    sep()
    insep = []
    for a, b in itertools.combinations(beads, 2):
        inter = dist_chroma2(means[a], means[b])
        sp_a  = chroma_devs.get(a, 0.0)
        sp_b  = chroma_devs.get(b, 0.0)
        eff   = inter - sp_a - sp_b
        if eff <= 0:
            insep.append((a, b, eff))
        warn = "  ← INSEPARABLE" if eff <= 0 else \
               ("  ← tight" if eff < 0.005 else "")
        if eff < 0.015 or eff <= 0:
            print(f"    {a:>5d} vs {b:>3d}  {inter:>10.5f}  {sp_a:>9.5f}  "
                  f"{sp_b:>9.5f}  {eff:>9.5f}{warn}")

    if insep:
        print(f"\n  !! {len(insep)} inseparable pair(s) in Chroma2.")
    else:
        print(f"\n  All Chroma2 pairs have positive effective margin.")


# ── Formatting helpers ────────────────────────────────────────────────────────

def sep(char="─", width=62):
    print(char * width)


# ── Main ──────────────────────────────────────────────────────────────────────

def main():
    ap = argparse.ArgumentParser(
        description="Analyse BeadCalibrate.ino CSV — find best gain + colour space.")
    ap.add_argument("csv_file", help="CSV file produced by BeadCalibrate.ino")
    ap.add_argument("--gain", default=None,
                    help="Restrict analysis to one gain label, e.g. g16x")
    ap.add_argument("--top", type=int, default=10,
                    help="Number of closest bead pairs to list (default 10)")
    ap.add_argument("--min-samples", type=int, default=2,
                    help="Exclude beads with fewer than N samples (default 2). "
                         "Filters out single-shot calibration/wiggle entries.")
    args = ap.parse_args()

    rows = parse_csv(args.csv_file)
    if not rows:
        print("No data found.  Check path and CSV format.", file=sys.stderr)
        sys.exit(1)

    all_gains   = sorted({r["gain"] for r in rows})
    all_beads   = sorted({r["bead"] for r in rows})
    gains_todo  = [args.gain] if args.gain else all_gains

    print(f"\nLoaded {len(rows)} rows | {len(all_beads)} beads | "
          f"gains: {', '.join(all_gains)}")

    # ── 1. Saturation summary ──────────────────────────────────────────────────
    sep("═")
    print("SATURATION SUMMARY  (saturated rows are excluded from analysis)")
    sep("═")
    print(f"  {'Gain':8s}  {'Saturated':>12s}  {'Total':>8s}  {'%':>5s}")
    sep()
    for gain in all_gains:
        total = [r for r in rows if r["gain"] == gain]
        sat   = [r for r in total if r["sat"]]
        pct   = 100.0 * len(sat) / max(len(total), 1)
        flag  = "  ← SATURATED" if pct > 20 else ""
        print(f"  {gain:8s}  {len(sat):>12d}  {len(total):>8d}  {pct:>4.0f}%{flag}")
    print()

    # Collect per-gain colour-space metrics for the cross-gain comparison table.
    cross_gain_scores = {}   # gain → {cs_name: min_dist}
    cross_gain_snr    = {}   # gain → {cs_name: SNR}

    # ── 2. Per-gain deep analysis ──────────────────────────────────────────────
    for gain in gains_todo:
        sep("═")
        print(f"GAIN: {gain}")
        sep("═")

        means = compute_bead_means(rows, gain)
        # Drop beads with too few samples (e.g. single-shot wiggle/calibration entries).
        means = {b: m for b, m in means.items() if m["n"] >= args.min_samples}
        if len(means) < 2:
            print(f"  Fewer than 2 beads with ≥{args.min_samples} samples at gain {gain}. Skipping.\n")
            continue

        # ── 2a. Per-bead averages ──────────────────────────────────────────────
        print(f"\nPer-bead mean values  (n = samples used, excl. saturated)")
        sep()
        hdr = (f"  {'Bead':>5}  {'H':>7}  {'S':>7}  {'L':>7}  "
               f"{'chR':>7}  {'chG':>7}  {'chB':>7}  {'n':>3}")
        print(hdr)
        sep()
        for bead, m in sorted(means.items()):
            print(f"  {bead:5d}  {m['H']:7.4f}  {m['S']:7.4f}  {m['L']:7.4f}  "
                  f"{m['chroma_r']:7.4f}  {m['chroma_g']:7.4f}  {m['chroma_b']:7.4f}  {m['n']:3d}")

        # ── 2b. Intra-bead noise ──────────────────────────────────────────────
        noise_key = "std_H"
        noisy = {b: m for b, m in means.items() if noise_key in m}
        if noisy:
            avg_std_H = statistics.mean(m["std_H"] for m in noisy.values())
            avg_std_S = statistics.mean(m.get("std_S", 0) for m in noisy.values())
            avg_std_L = statistics.mean(m.get("std_L", 0) for m in noisy.values())
            avg_std_chR = statistics.mean(m.get("std_chroma_r", 0) for m in noisy.values())
            avg_std_chG = statistics.mean(m.get("std_chroma_g", 0) for m in noisy.values())
            print(f"\n  Average intra-bead std dev (noise):")
            print(f"    H={avg_std_H:.5f}  S={avg_std_S:.5f}  L={avg_std_L:.5f}"
                  f"  chR={avg_std_chR:.5f}  chG={avg_std_chG:.5f}")

        # ── 2c. Pairwise distances per colour space ───────────────────────────
        print(f"\nColour-space separability")
        print(f"  SNR = min inter-bead dist / intra-bead noise RMS  (scale-independent; higher = better)")
        sep()
        print(f"  {'Space':8s}  {'min dist':>10s}  {'noise RMS':>10s}  {'SNR':>6s}  closest pair")
        sep()
        cs_scores = {}
        cs_snr    = {}
        best_cs_name = None
        best_cs_snr  = -1.0
        for cs_name, dist_fn in COLOR_SPACES.items():
            pairs = pairwise_distances(means, dist_fn)
            min_d, ba, bb = pairs[0]
            nrms = cs_noise_rms(means, cs_name)
            snr  = min_d / nrms if (nrms > 0 and not math.isnan(nrms)) else float("nan")
            cs_scores[cs_name] = min_d
            cs_snr[cs_name]    = snr
            snr_str = f"{snr:6.1f}" if not math.isnan(snr) else "   n/a"
            print(f"  {cs_name:8s}  {min_d:10.5f}  {nrms:10.5f}  {snr_str}  beads {ba} vs {bb}")
            if not math.isnan(snr) and snr > best_cs_snr:
                best_cs_snr  = snr
                best_cs_name = cs_name

        cross_gain_scores[gain] = cs_scores
        cross_gain_snr[gain]    = cs_snr
        print(f"\n  ► Best colour space at this gain: {best_cs_name}"
              f"  (SNR = {best_cs_snr:.1f})")

        # ── 2d. Closest pairs in the best colour space ────────────────────────
        best_pairs = pairwise_distances(means, COLOR_SPACES[best_cs_name])
        best_nrms  = cs_noise_rms(means, best_cs_name)
        n_show = min(args.top, len(best_pairs))
        print(f"\n  Closest {n_show} bead pairs in {best_cs_name} space:")
        sep()
        for dist, ba, bb in best_pairs[:n_show]:
            pair_snr = dist / best_nrms if best_nrms > 0 else float("nan")
            warn = "  ← may collide" if (not math.isnan(pair_snr) and pair_snr < 3.0) else ""
            snr_str = f"  SNR={pair_snr:.1f}" if not math.isnan(pair_snr) else ""
            print(f"    beads {ba:3d} vs {bb:3d}  dist = {dist:.5f}{snr_str}{warn}")

        # ── 2e. Threshold suggestions (inter-bead only — upper bound) ─────────
        thH, thS, thL = suggest_hsl_thresholds(means)
        thCh = suggest_chroma_threshold(means)
        print(f"\n  Inter-bead upper-bound thresholds  (half the min per-channel gap):")
        print(f"    HSL:       thresholdH = {thH:.4f}  "
              f"thresholdS = {thS:.4f}  thresholdL = {thL:.4f}")
        print(f"    Chroma2:   threshold  = {thCh:.4f}")
        print(f"  NOTE: these are the TIGHTEST permissible thresholds (upper bound).")
        print(f"  They may be smaller than the intra-bead spread — see section below.")

        # ── 2f. Keep-together / keep-apart feasibility ────────────────────────
        sep("═")
        print(f"CLASSIFICATION FEASIBILITY  (gain: {gain})")
        print(f"  For each channel/space the threshold must satisfy:")
        print(f"    min_T  = max intra-bead sample spread   (keep same bead together)")
        print(f"    max_T  = half min inter-bead mean gap   (keep different beads apart)")
        print(f"  A feasible threshold exists only when min_T < max_T.")
        print(f"  The AND-logic of BeadSorter means ONE channel gap is enough to")
        print(f"  separate a pair — so per-pair effective margin uses the best channel.")
        sep("═")

        hsl_devs    = compute_hsl_deviations(rows, gain, means)
        chroma_devs = compute_chroma2_deviations(rows, gain, means)

        hsl_classification_analysis(means, hsl_devs)
        print()
        chroma2_classification_analysis(means, chroma_devs)
        print()

    # ── 3. Cross-gain comparison ───────────────────────────────────────────────
    if len(gains_todo) > 1 and len(cross_gain_snr) >= 2:
        sep("═")
        print("CROSS-GAIN COMPARISON  (SNR = min inter-bead dist / noise RMS — higher = better)")
        print("  Raw distances are on different scales per colour space and cannot be compared")
        print("  directly. SNR is dimensionless and scale-independent.")
        sep("═")
        cs_names = list(COLOR_SPACES.keys())
        header = f"  {'Gain':8s}" + "".join(f"  {n:>8s}" for n in cs_names)
        print(header)
        sep()
        for gain in gains_todo:
            if gain not in cross_gain_snr:
                continue
            row_str = f"  {gain:8s}"
            row_str += "".join(
                f"  {cross_gain_snr[gain].get(n, float('nan')):>8.1f}"
                for n in cs_names
            )
            print(row_str)

        # Best overall combination — highest SNR across all gain×space combos.
        best_gain = max(
            cross_gain_snr,
            key=lambda g: max(
                (v for v in cross_gain_snr[g].values() if not math.isnan(v)),
                default=0.0
            )
        )
        best_cs_all = max(
            COLOR_SPACES,
            key=lambda cs: cross_gain_snr.get(best_gain, {}).get(cs, 0.0)
        )
        gain_enum = {
            "g1x":  "TCS34725_GAIN_1X",
            "g4x":  "TCS34725_GAIN_4X",
            "g16x": "TCS34725_GAIN_16X",
            "g60x": "TCS34725_GAIN_60X",
        }
        best_snr = cross_gain_snr.get(best_gain, {}).get(best_cs_all, float("nan"))
        print()
        sep("═")
        print(f"RECOMMENDATION  (based on best SNR)")
        sep("═")
        print(f"  Best gain:         {best_gain}")
        print(f"  Best colour space: {best_cs_all}  (SNR = {best_snr:.1f})")
        print()
        print(f"  If switching gain in BeadSorter.ino:")
        print(f"    Adafruit_TCS34725 tcs = Adafruit_TCS34725(")
        print(f"        TCS34725_INTEGRATIONTIME_101MS,")
        print(f"        {gain_enum.get(best_gain, best_gain)});")

        # Print best-gain thresholds one more time.
        best_means = {b: m for b, m in compute_bead_means(rows, best_gain).items()
                      if m["n"] >= args.min_samples}
        if len(best_means) >= 2:
            thH, thS, thL = suggest_hsl_thresholds(best_means)
            thCh = suggest_chroma_threshold(best_means)
            print()
            print(f"  HSL thresholds at {best_gain}:")
            print(f"    float thresholdH = {thH:.4f};")
            print(f"    float thresholdS = {thS:.4f};")
            print(f"    float thresholdL = {thL:.4f};")
            print()
            print(f"  Chroma2 threshold at {best_gain}:  {thCh:.4f}")
            print(f"  (Store chroma_r and chroma_g per colour and compare with"
                  f" dist = sqrt(dCR²+dCG²))")
        print()


if __name__ == "__main__":
    main()
